Forestierr/Light_trainer/1_Documentation/Digi-Key_ Panier_files/ESP32-DEVKITC-32D_sml.jpg

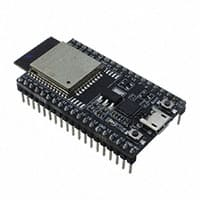
1_Documentation/Digi-Key_ Panier_files/ESP32-DEVKITC-32D_sml.jpg
