Forestierr/Light_trainer/1_Documentation/Digi-Key_ Panier_files/0805-(1.40)-CL-Series_sml.jpg

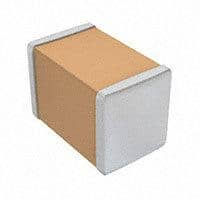
1_Documentation/Digi-Key_ Panier_files/0805-(1.40)-CL-Series_sml.jpg
