Forestierr/Light_trainer/1_Documentation/Digi-Key_ Panier_files/1101M2S5CQE2_sml.jpg

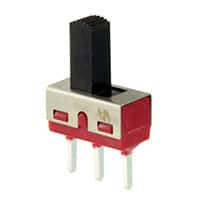
1_Documentation/Digi-Key_ Panier_files/1101M2S5CQE2_sml.jpg
