Forestierr/Light_trainer/1_Documentation/Digi-Key_ Panier_files/1210-(3225-Metric)-2,70mm_sml.jpg

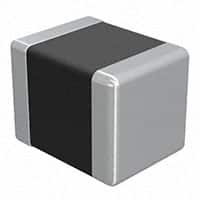
1_Documentation/Digi-Key_ Panier_files/1210-(3225-Metric)-2,70mm_sml.jpg
