Forestierr/Light_trainer/1_Documentation/Digi-Key_ Panier_files/1655_sml.JPG

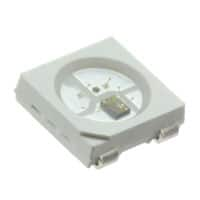
1_Documentation/Digi-Key_ Panier_files/1655_sml.JPG
