Forestierr/Light_trainer/1_Documentation/Digi-Key_ Panier_files/2464_sml.jpg

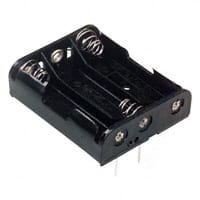
1_Documentation/Digi-Key_ Panier_files/2464_sml.jpg
