Forestierr/Light_trainer/1_Documentation/Digi-Key_ Panier_files/MX1A-11NW_sml.jpg

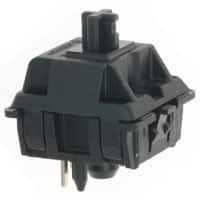
1_Documentation/Digi-Key_ Panier_files/MX1A-11NW_sml.jpg
