Forestierr/Light_trainer/1_Documentation/Digi-Key_ Panier_files/new_chat_bubble_1.jpg

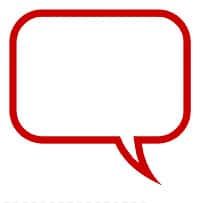
1_Documentation/Digi-Key_ Panier_files/new_chat_bubble_1.jpg
