Forestierr/Light_trainer/1_Documentation/Digi-Key_ Panier_files/RNCP1206FTD2K80_sml.jpg

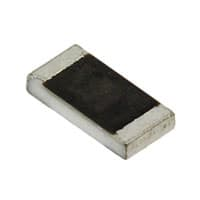
1_Documentation/Digi-Key_ Panier_files/RNCP1206FTD2K80_sml.jpg
