Forestierr/Light_trainer/1_Documentation/Digi-Key_ Panier_files/SOT223-3_sml.jpg

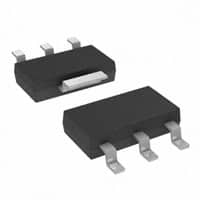
1_Documentation/Digi-Key_ Panier_files/SOT223-3_sml.jpg
