Forestierr/Light_trainer/1_Documentation/DOC_FAB/PDF_GERBER_BOT_3D.PNG

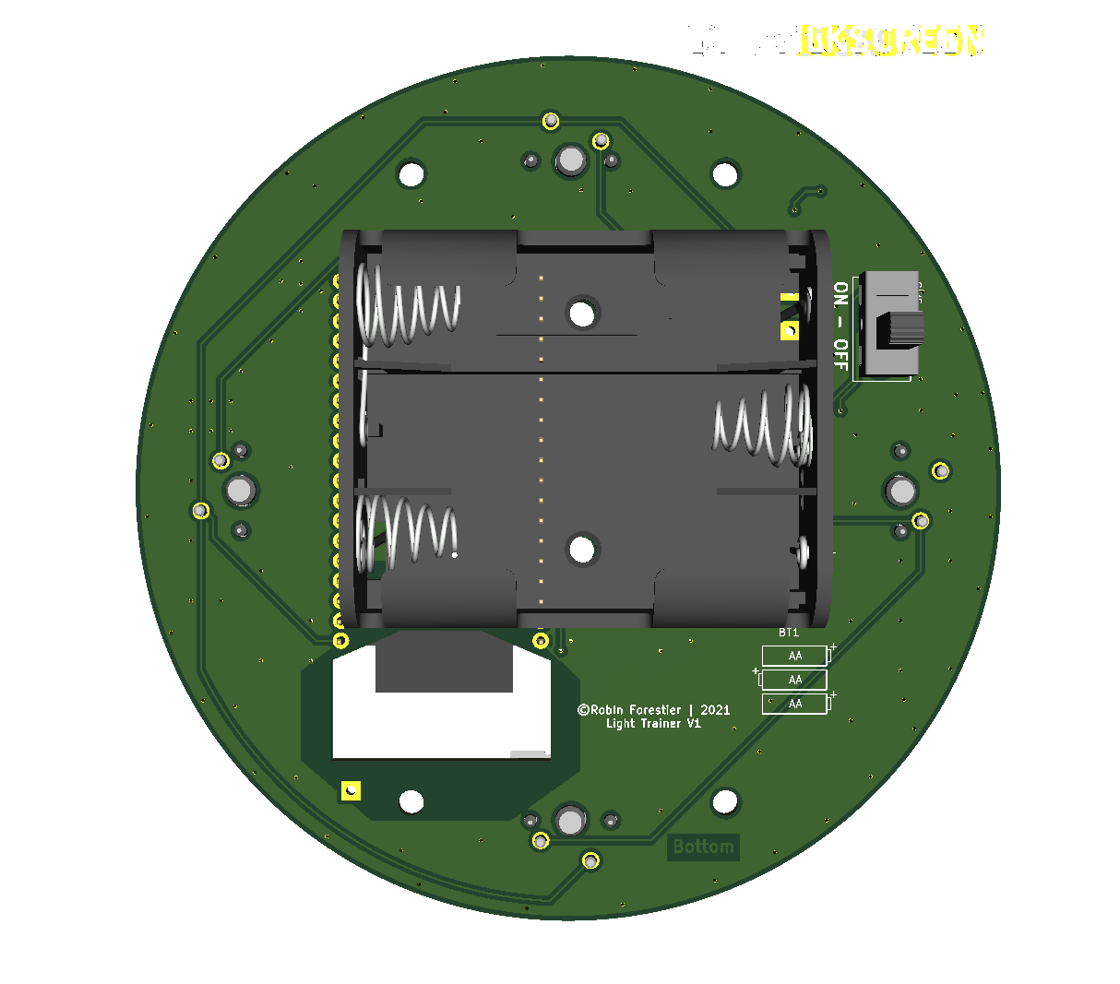
1_Documentation/DOC_FAB/PDF_GERBER_BOT_3D.PNG
