Forestierr/Light_trainer/1_Documentation/DOC_FAB/PDF_GERBER_TOP_3D.PNG

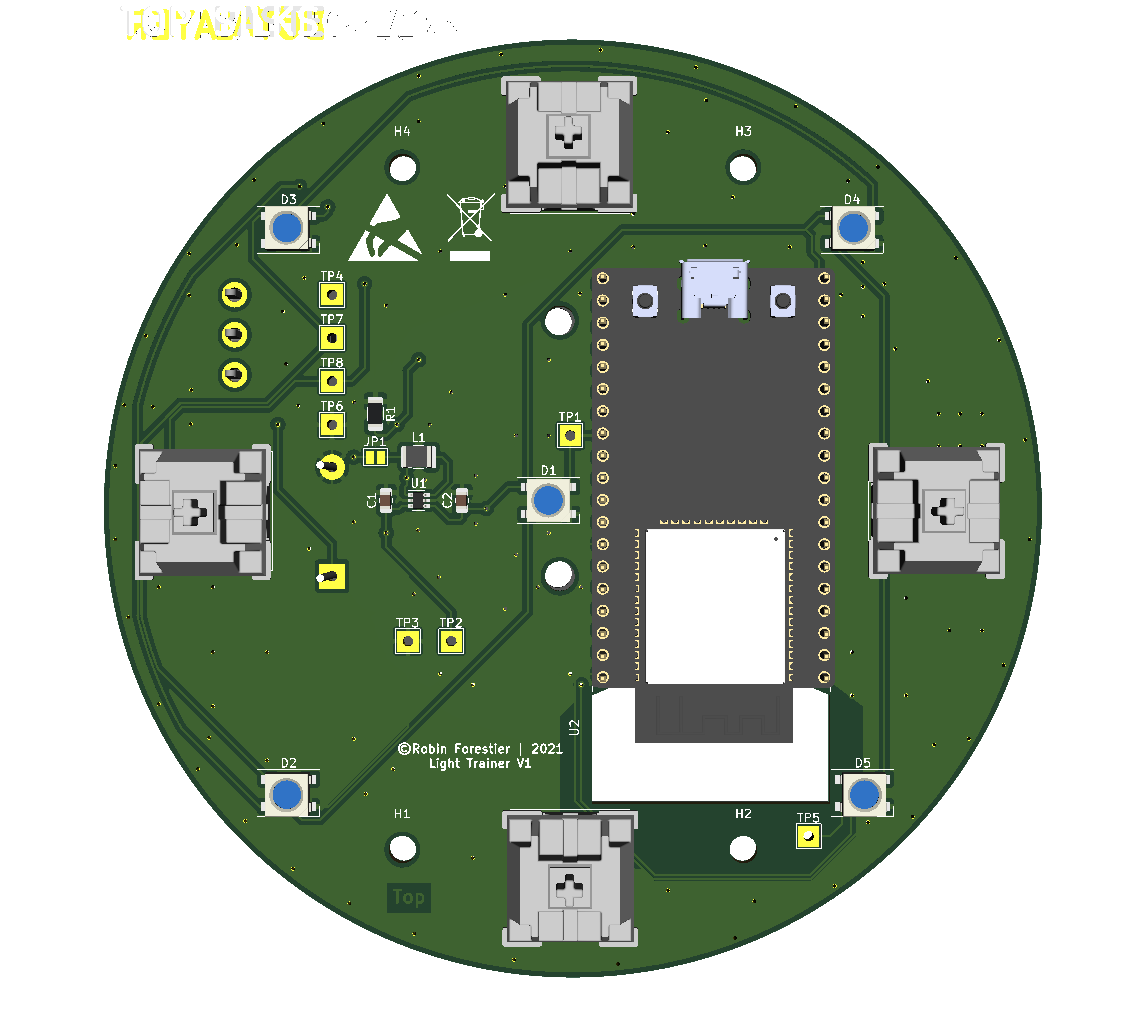
1_Documentation/DOC_FAB/PDF_GERBER_TOP_3D.PNG
