Forestierr/Light_trainer/1_Documentation/images/battery_connect.png

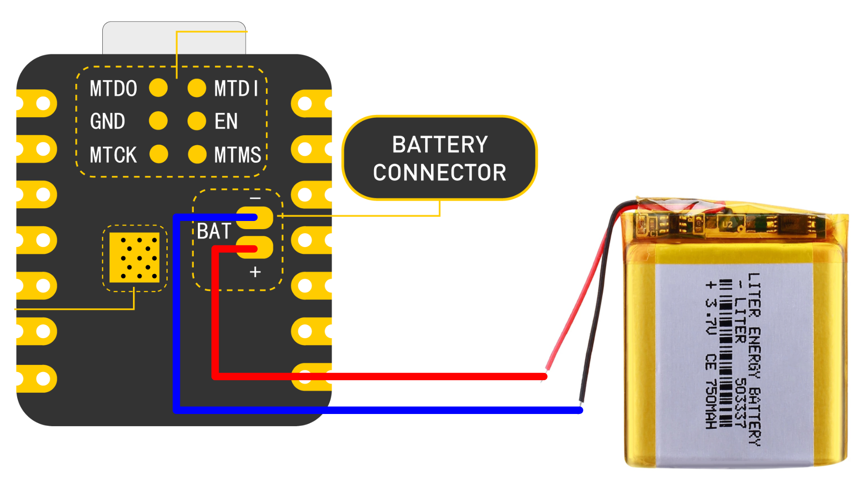
1_Documentation/images/battery_connect.png
