Forestierr/Light_trainer/1_Documentation/Photos/Conn_1.JPEG

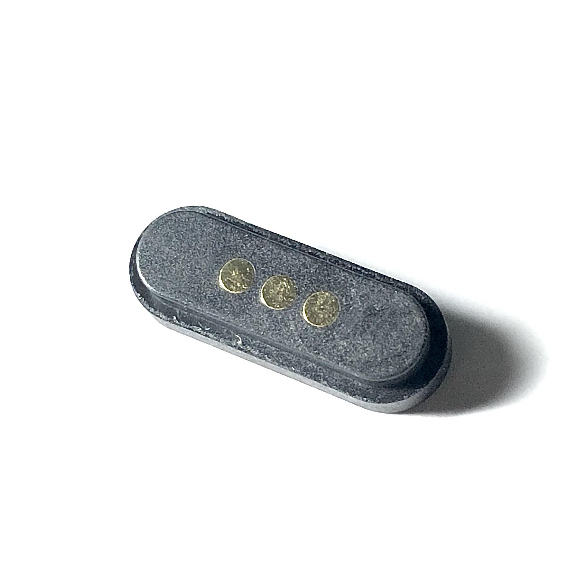
1_Documentation/Photos/Conn_1.JPEG
