Forestierr/Light_trainer/1_Documentation/Photos/Conn_4.JPEG

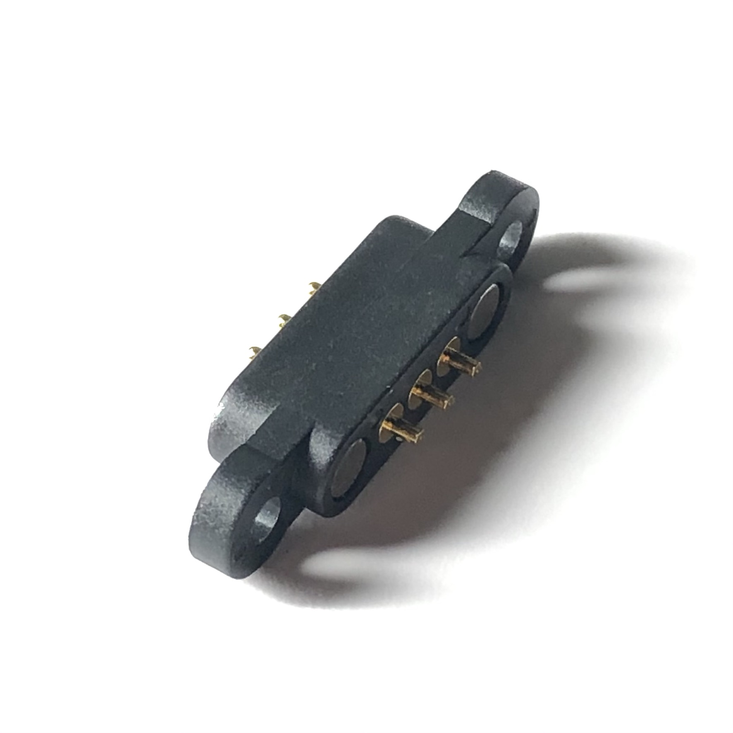
1_Documentation/Photos/Conn_4.JPEG
