Forestierr/Light_trainer/1_Documentation/Photos/Conn_5.JPEG

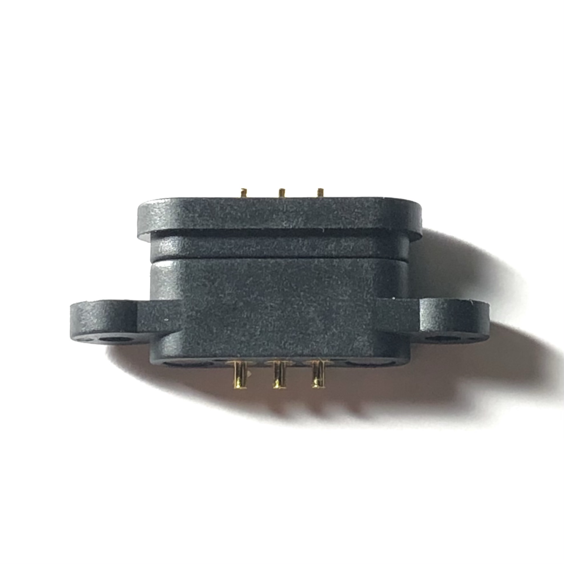
1_Documentation/Photos/Conn_5.JPEG
