Forestierr/Light_trainer/1_Documentation/Wiki/Alimentation.PNG

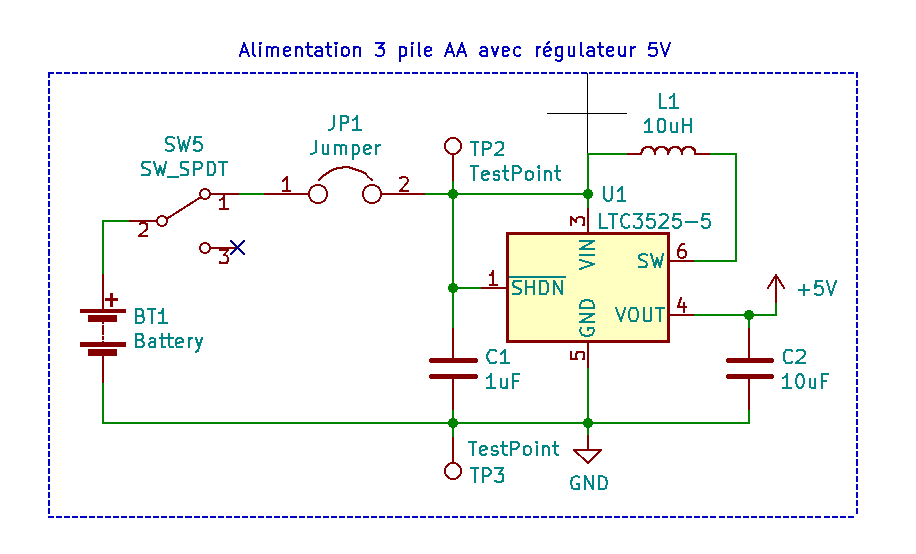
1_Documentation/Wiki/Alimentation.PNG
