Forestierr/Light_trainer/1_Documentation/Wiki/ESP.PNG

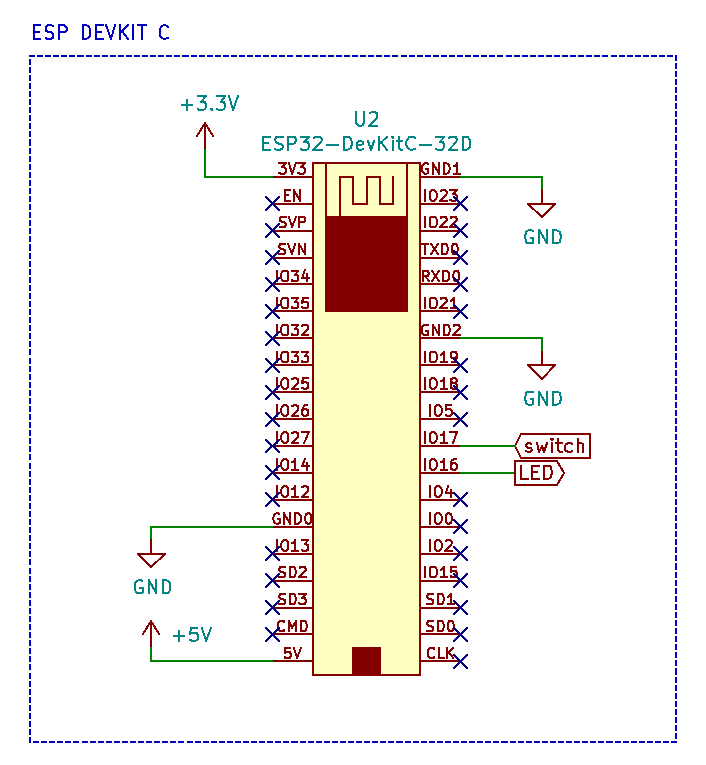
1_Documentation/Wiki/ESP.PNG
