Forestierr/Light_trainer/1_Documentation/Wiki/Led.PNG

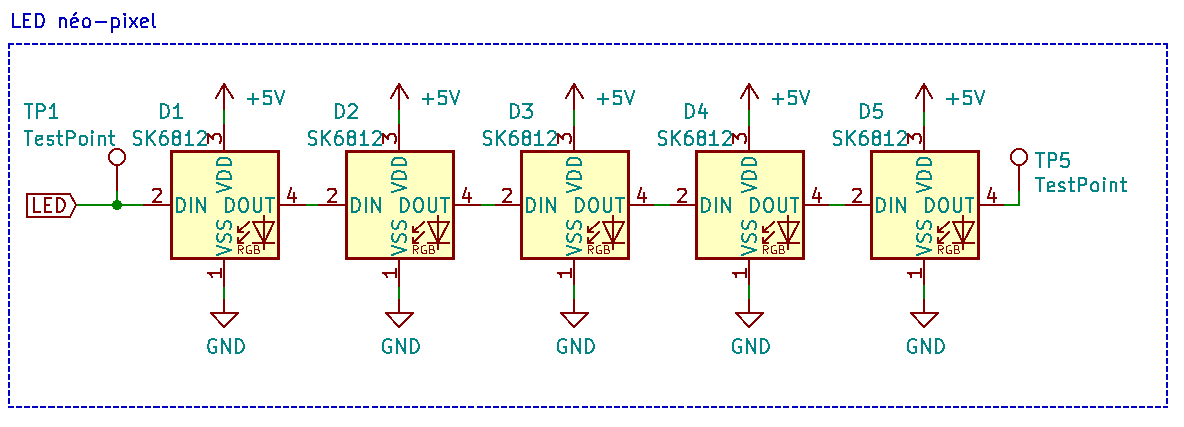
1_Documentation/Wiki/Led.PNG
