Forestierr/Light_trainer/1_Documentation/Wiki/MountingHolle.PNG

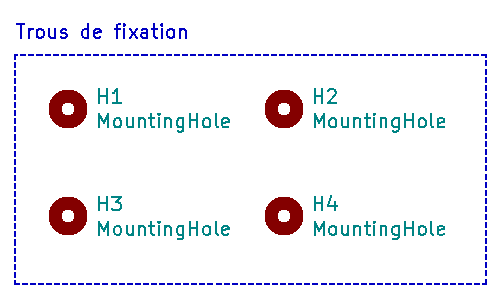
1_Documentation/Wiki/MountingHolle.PNG
