Forestierr/Light_trainer/1_Documentation/Wiki/PlanImplantation_1.jpg

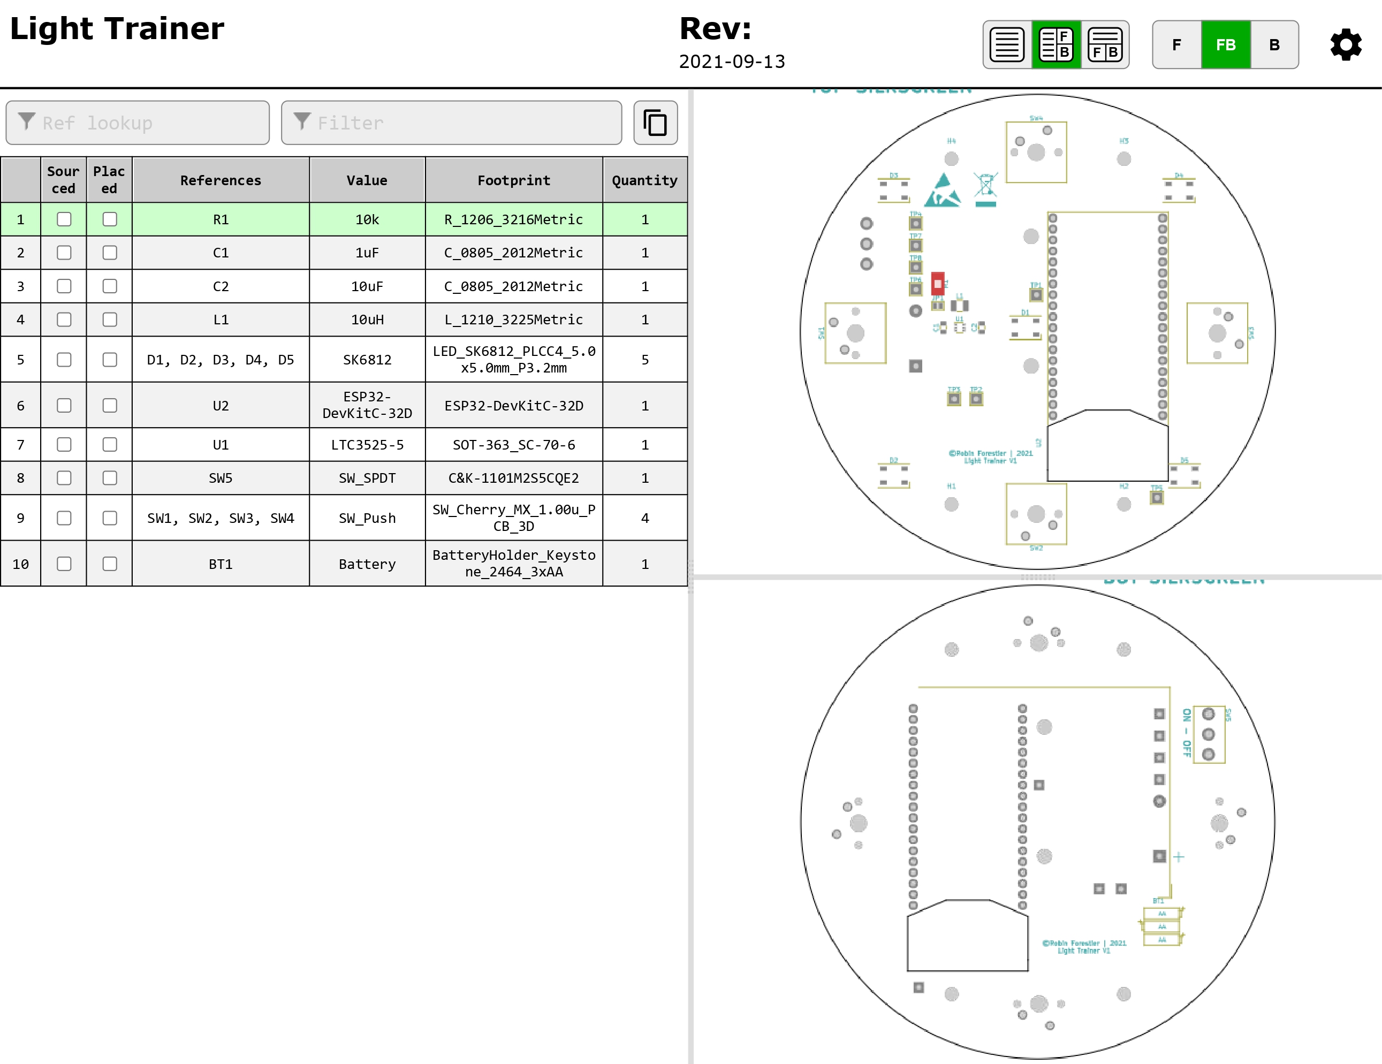
1_Documentation/Wiki/PlanImplantation_1.jpg
