Forestierr/Light_trainer/1_Documentation/Wiki/PlanImplantation_9.jpg

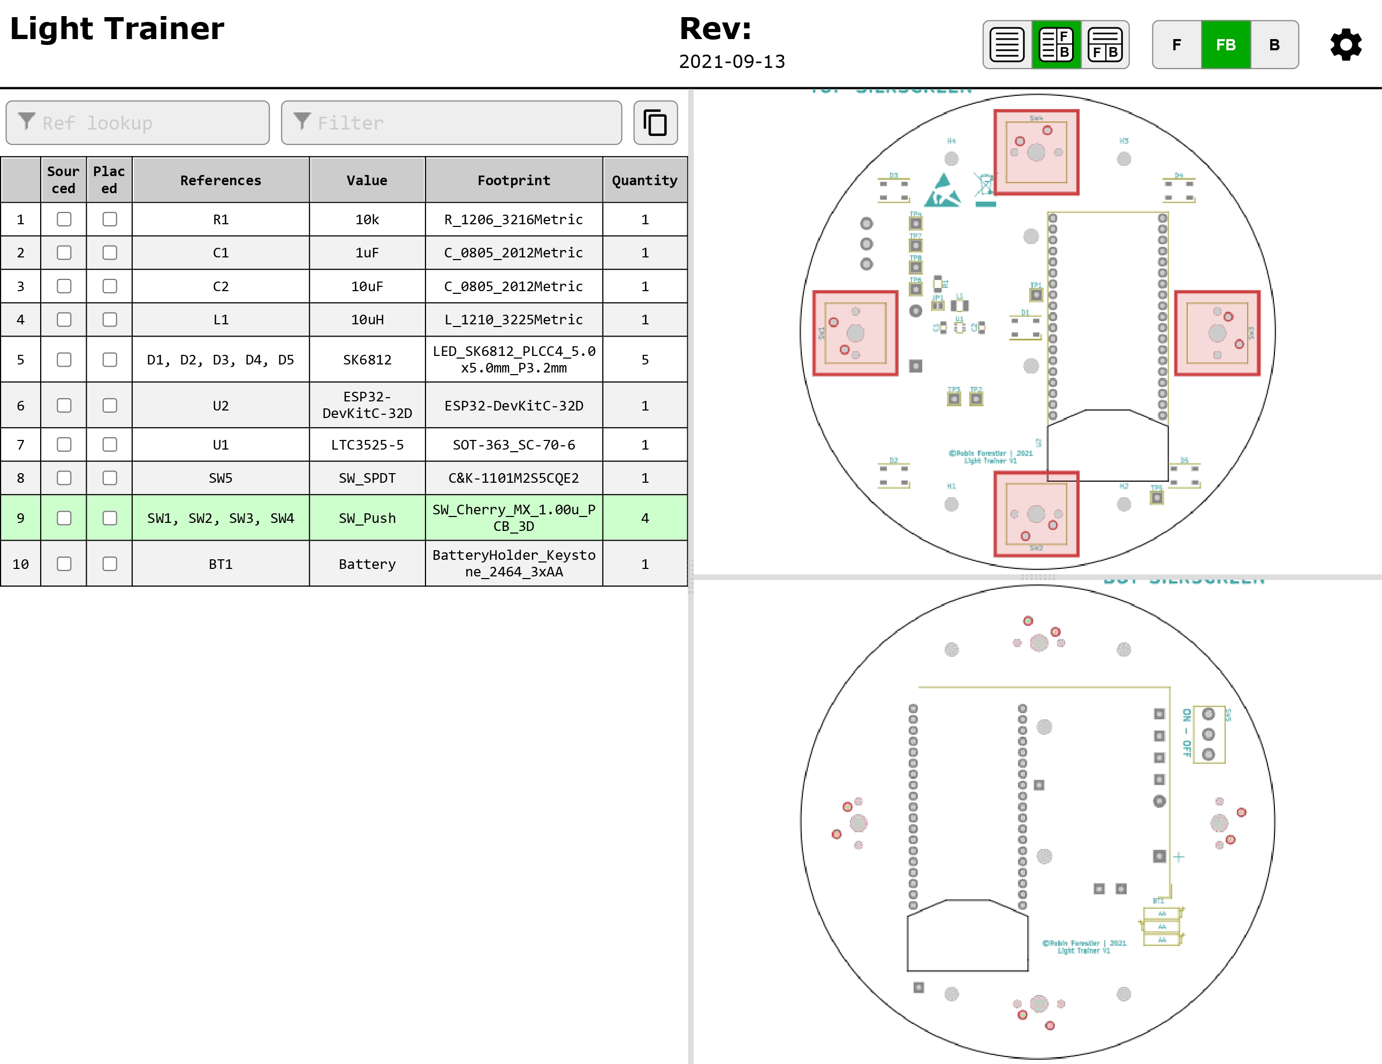
1_Documentation/Wiki/PlanImplantation_9.jpg
