Forestierr/Light_trainer/1_Documentation/Wiki/Switch.PNG

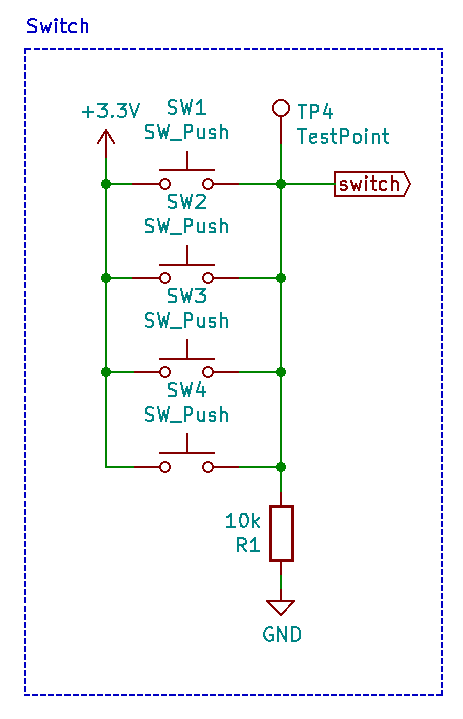
1_Documentation/Wiki/Switch.PNG
