Forestierr/Light_trainer/1_Documentation/Wiki/TestPoint.PNG

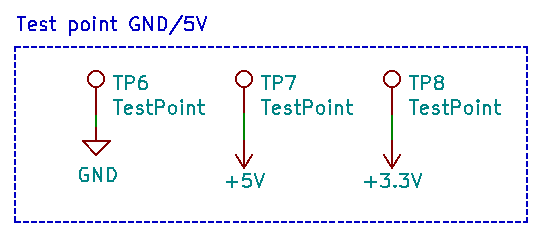
1_Documentation/Wiki/TestPoint.PNG
