Forestierr/Light_trainer/1_Documentation/DOC_FAB/PlanImplantation/PlanImplantation_1_10.pdf

Ref lookup | Filter
Light Trainer | Rev:

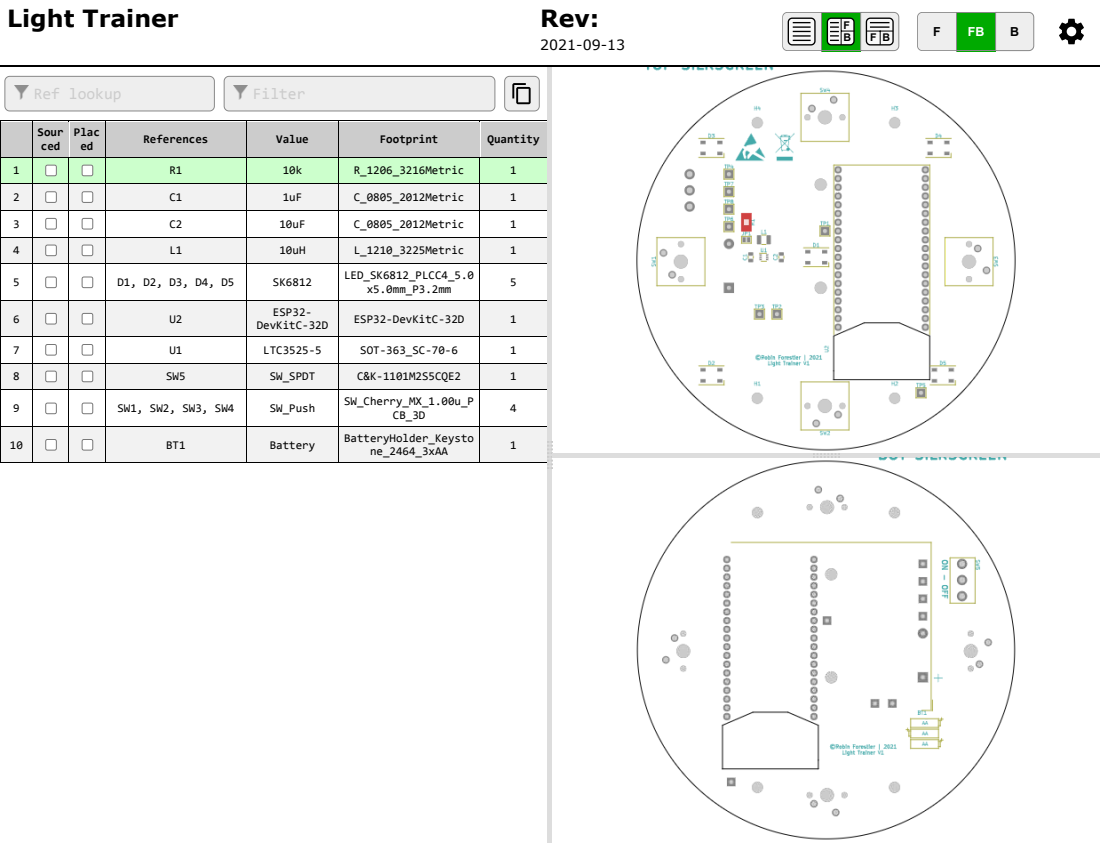
[picture p43: page 1]

Sour ced | Plac ed | References | Value | Footprint | Quantity

1 | | | R1 | 10k | R_1206_3216Metric | 1
2 | | | C1 | 1uF | C_0805_2012Metric | 1
3 | | | C2 | 10uF | C_0805_2012Metric | 1
4 | | | L1 | 10uH | L_1210_3225Metric | 1
5 | | | D1, D2, D3, D4, D5 | SK6812 | LED_SK6812_PLCC4_5.0 x5.0mm_P3.2mm | 5

6 | | | U2 | ESP32-DevKitC-32D | ESP32-DevKitC-32D | 1

7 | | | U1 | LTC3525-5 | SOT-363_SC-70-6 | 1
8 | | | SW5 | SW_SPDT | C&K-1101M2S5CQE2 | 1
9 | | | SW1, SW2, SW3, SW4 | SW_Push | SW_Cherry_MX_1.00u_P CB_3D | 4

10 | | | BT1 | Battery | BatteryHolder_Keysto ne_2464_3xAA | 1

Ref lookup | Filter

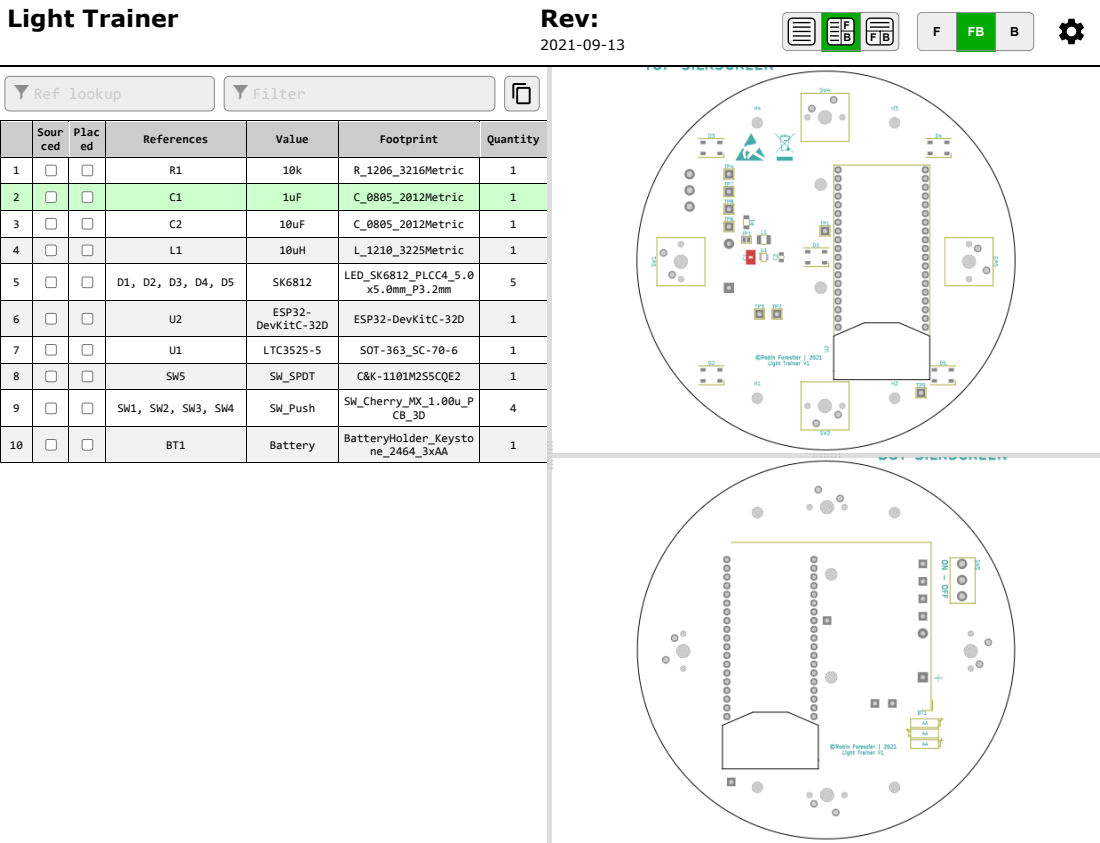
[picture p44: page 2]

Sour ced | Plac ed | References | Value | Footprint | Quantity

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

6 | | | U2 | ESP32-DevKitC-32D | ESP32-DevKitC-32D | 1

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

10 | | | BT1 | Battery | BatteryHolder_Keysto ne_2464_3xAA | 1

Ref lookup | Filter

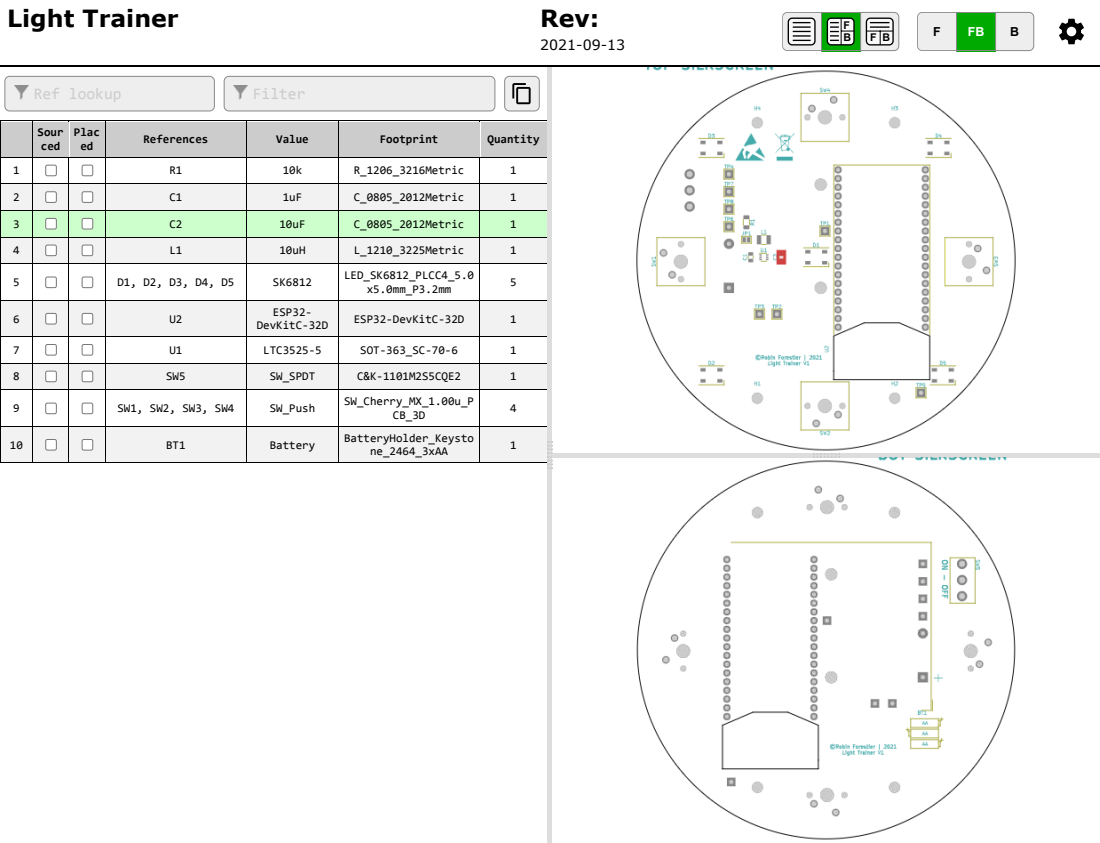
[picture p45: page 3]

Sour ced | Plac ed | References | Value | Footprint | Quantity

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

6 | | | U2 | ESP32-DevKitC-32D | ESP32-DevKitC-32D | 1

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

10 | | | BT1 | Battery | BatteryHolder_Keysto ne_2464_3xAA | 1

Ref lookup | Filter

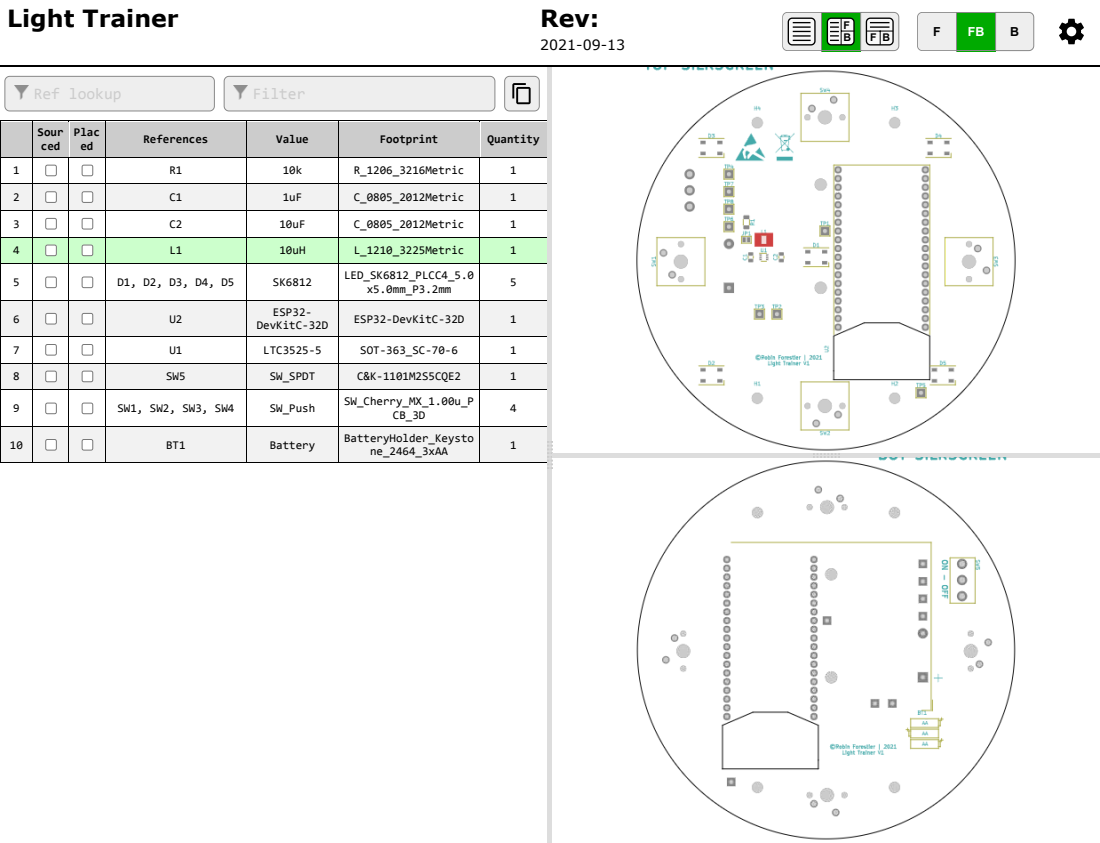
[picture p46: page 4]

Sour ced | Plac ed | References | Value | Footprint | Quantity

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

6 | | | U2 | ESP32-DevKitC-32D | ESP32-DevKitC-32D | 1

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

10 | | | BT1 | Battery | BatteryHolder_Keysto ne_2464_3xAA | 1

Ref lookup | Filter

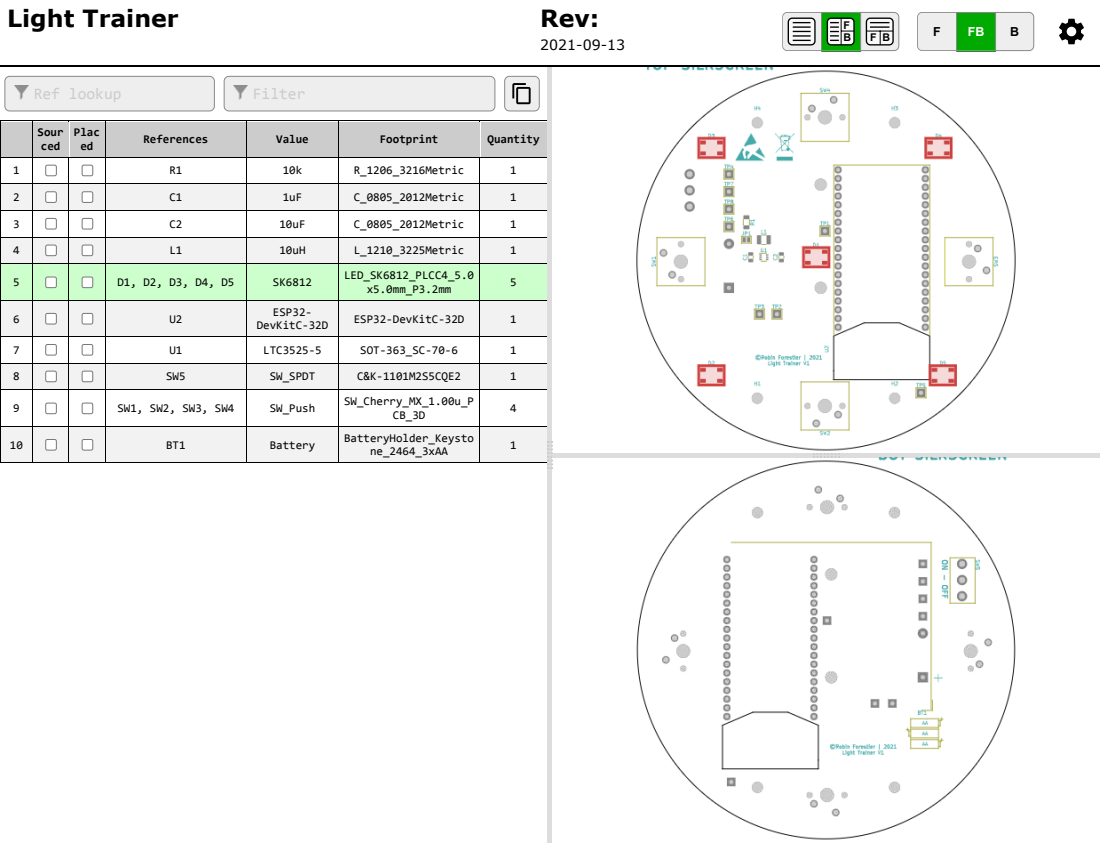
[picture p47: page 5]

Sour ced | Plac ed | References | Value | Footprint | Quantity

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

6 | | | U2 | ESP32-DevKitC-32D | ESP32-DevKitC-32D | 1

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

10 | | | BT1 | Battery | BatteryHolder_Keysto ne_2464_3xAA | 1

Ref lookup | Filter

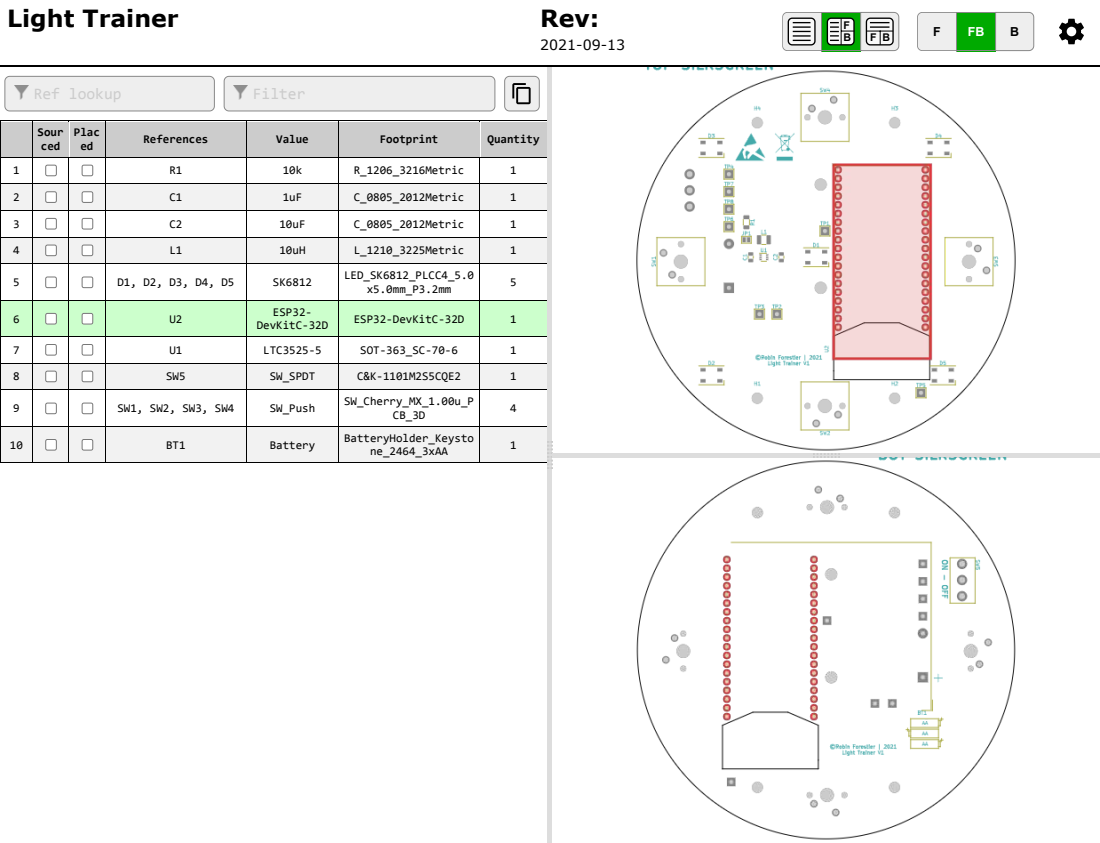
[picture p48: page 6]

Sour ced | Plac ed | References | Value | Footprint | Quantity

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

6 | | | U2 | ESP32-DevKitC-32D | ESP32-DevKitC-32D | 1

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

10 | | | BT1 | Battery | BatteryHolder_Keysto ne_2464_3xAA | 1

Ref lookup | Filter

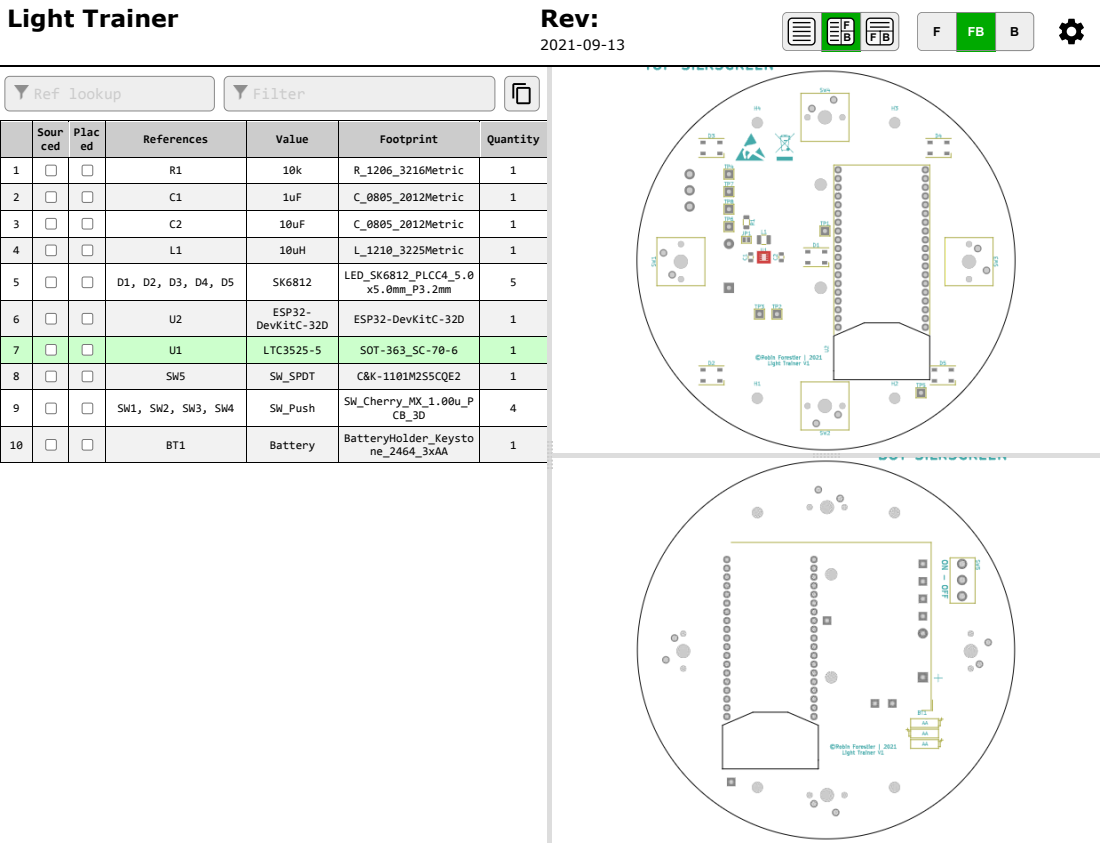
[picture p49: page 7]

Sour ced | Plac ed | References | Value | Footprint | Quantity

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

6 | | | U2 | ESP32-DevKitC-32D | ESP32-DevKitC-32D | 1

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

10 | | | BT1 | Battery | BatteryHolder_Keysto ne_2464_3xAA | 1

Ref lookup | Filter

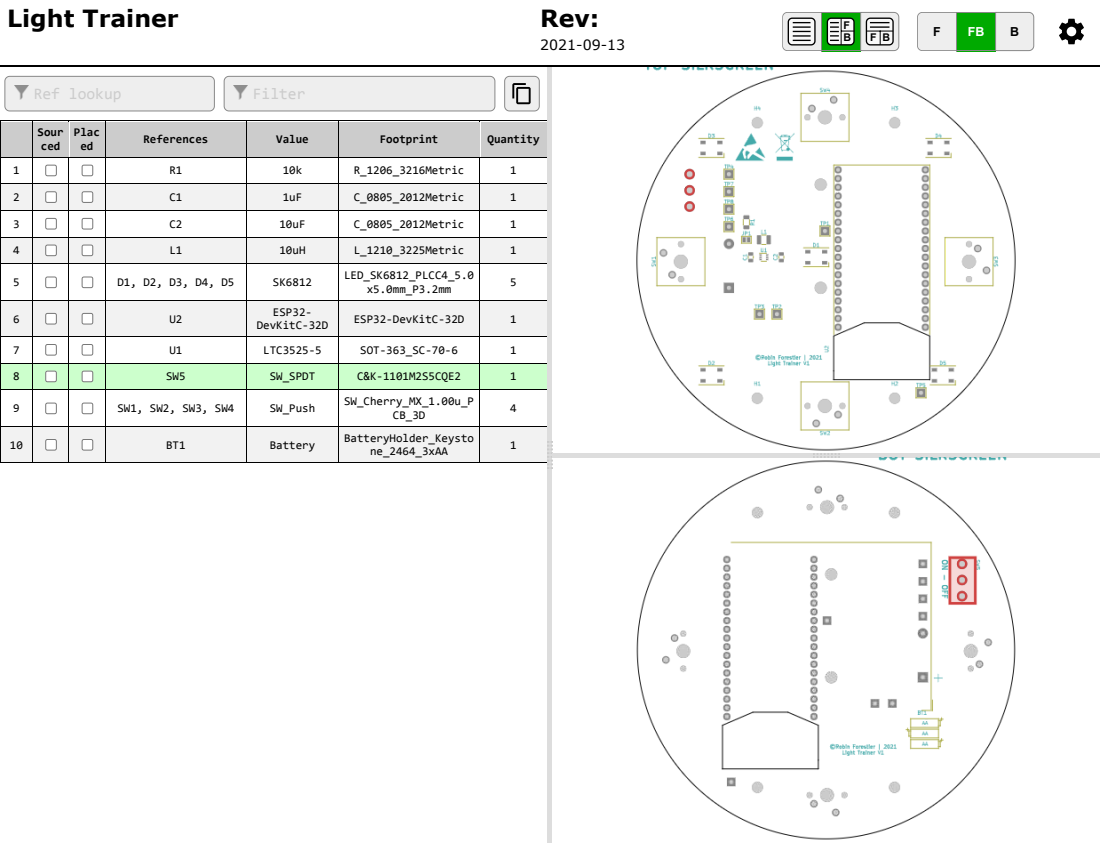
[picture p50: page 8]

Sour ced | Plac ed | References | Value | Footprint | Quantity

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

6 | | | U2 | ESP32-DevKitC-32D | ESP32-DevKitC-32D | 1

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

10 | | | BT1 | Battery | BatteryHolder_Keysto ne_2464_3xAA | 1

Ref lookup | Filter

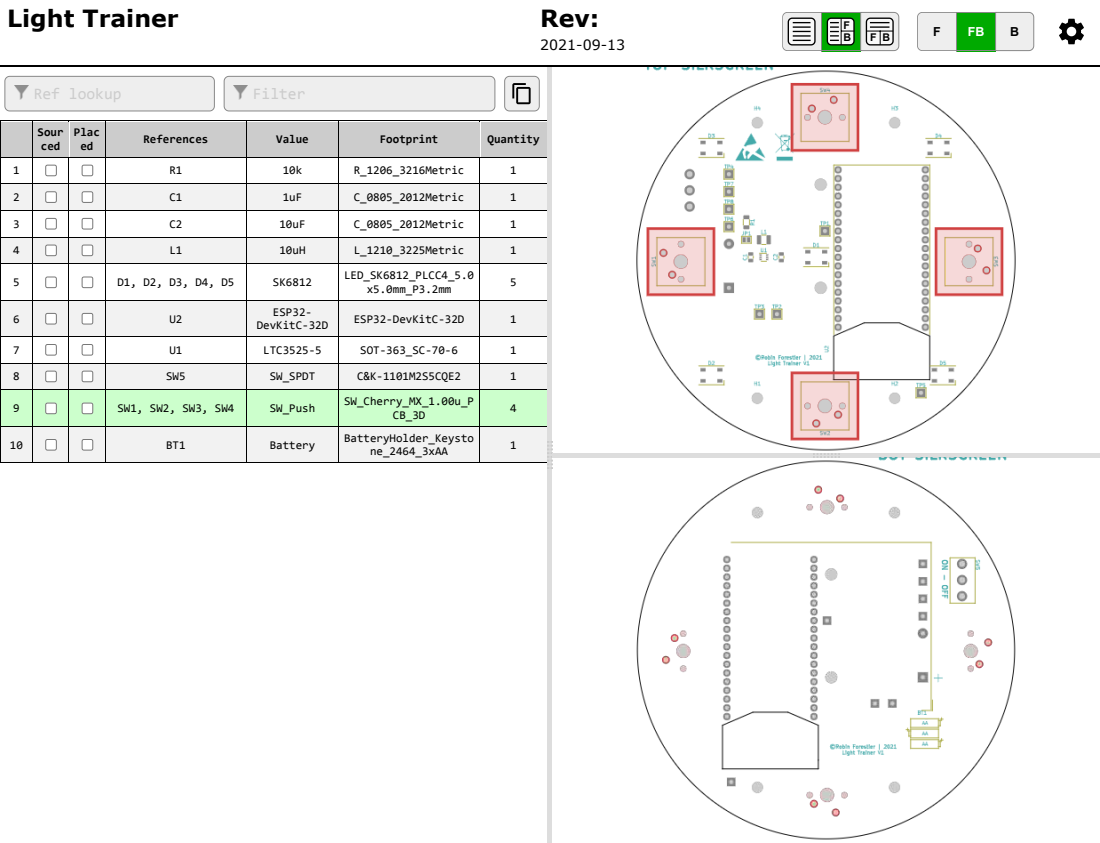
[picture p51: page 9]

Sour ced | Plac ed | References | Value | Footprint | Quantity

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

6 | | | U2 | ESP32-DevKitC-32D | ESP32-DevKitC-32D | 1

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

10 | | | BT1 | Battery | BatteryHolder_Keysto ne_2464_3xAA | 1

Ref lookup | Filter

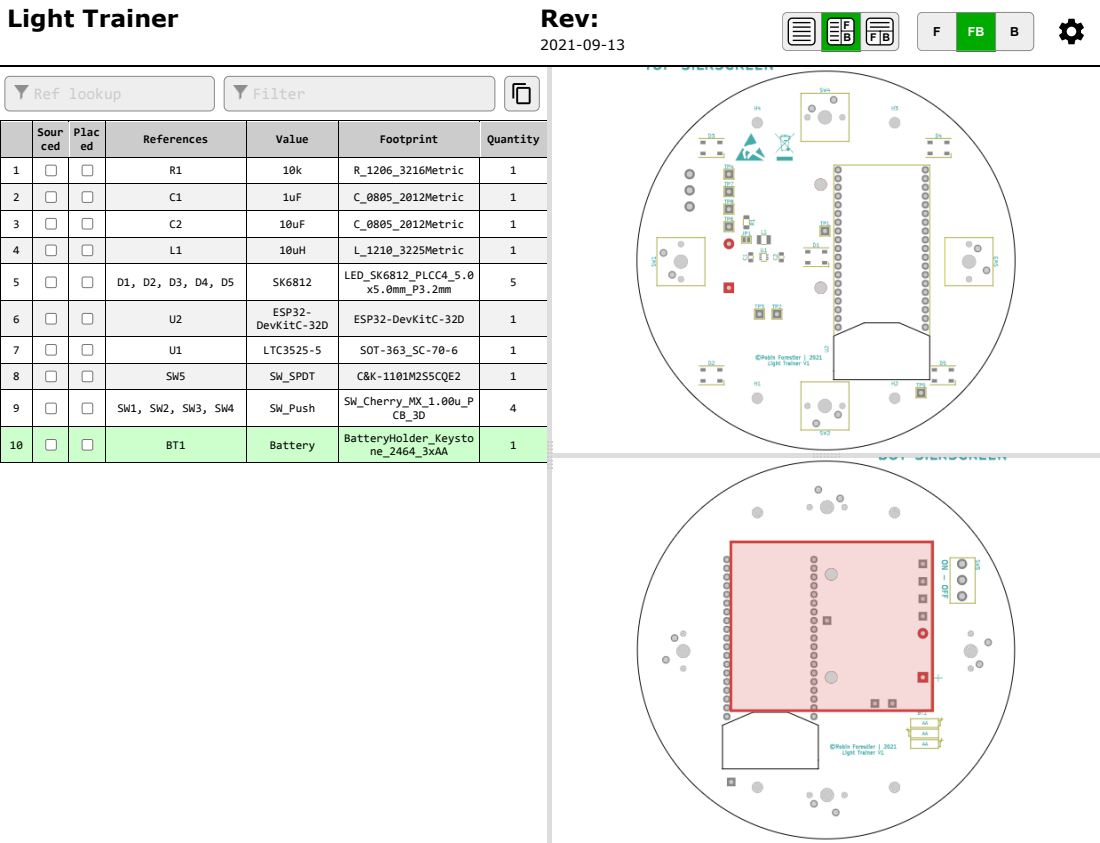
[picture p52: page 10]

Sour ced | Plac ed | References | Value | Footprint | Quantity

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

6 | | | U2 | ESP32-DevKitC-32D | ESP32-DevKitC-32D | 1

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

10 | | | BT1 | Battery | BatteryHolder_Keysto ne_2464_3xAA | 1
