Forestierr/Light_trainer/5_Programmation/XIAO-esp32-v3/main/DashboardHtml.h

#ifndef DASHBOARDHTML_H
#define DASHBOARDHTML_H

#include <Arduino.h>

// Dashboard Web Light Trainer - HTML5/CSS3/JS pré-compressé GZIP
// Taille originale: 84219 octets | Taille GZIP: 18264 octets (21.7%)
const size_t DASHBOARD_HTML_GZ_LEN = 18264;
const uint8_t DASHBOARD_HTML_GZ[] PROGMEM = {
  0x1F, 0x8B, 0x08, 0x00, 0x00, 0x00, 0x00, 0x00, 0x02, 0xFF, 0xED, 0x7D, 0x5D, 0x73, 0xDB, 0x48,
  0x92, 0xE0, 0xBB, 0x7F, 0x45, 0x99, 0xD3, 0xDD, 0x24, 0xC7, 0x22, 0x45, 0x80, 0xA4, 0x2C, 0x4B,
  0xB6, 0xE6, 0x64, 0x89, 0xB6, 0x35, 0x2B, 0x59, 0x5A, 0x91, 0xF6, 0x6C, 0x6F, 0x47, 0x5F, 0x1B,
  0x22, 0x21, 0x12, 0xD3, 0x20, 0xC1, 0x01, 0x40, 0x59, 0x6A, 0x8F, 0x22, 0xFA, 0xE5, 0x22, 0xAE,
  0xEF, 0x1E, 0x2E, 0xE2, 0x6E, 0x9F, 0x36, 0x36, 0x62, 0xF7, 0x36, 0xEE, 0x61, 0x7C, 0x0F, 0xF7,
  0x7C, 0x77, 0xAF, 0xFA, 0x27, 0xFD, 0x07, 0xEE, 0x7E, 0xC2, 0x65, 0x66, 0x15, 0x80, 0x2A, 0xA0,
  0x00, 0x82, 0xB2, 0xEC, 0x76, 0x5F, 0x4C, 0x7F, 0x50, 0x24, 0x50, 0x95, 0x95, 0x55, 0x95, 0x95,
  0x99, 0x95, 0x99, 0x95, 0xF5, 0xF8, 0xFE, 0xFE, 0xF1, 0xDE, 0xE0, 0xEB, 0x93, 0x1E, 0x9B, 0x84,
  0x53, 0x77, 0xE7, 0xDE, 0x63, 0xFC, 0xC3, 0x5C, 0x6B, 0x36, 0x7E, 0x52, 0x39, 0xF7, 0x2B, 0xF8,
  0xC0, 0xB6, 0x46, 0x3B, 0xF7, 0x18, 0x7B, 0x3C, 0xB5, 0x43, 0x8B, 0x0D, 0x27, 0x96, 0x1F, 0xD8,
  0xE1, 0x93, 0xCA, 0xAB, 0xC1, 0xB3, 0xC6, 0x66, 0x25, 0x79, 0x31, 0xB3, 0xA6, 0xF6, 0x93, 0xCA,
  0x85, 0x63, 0xBF, 0x9D, 0x7B, 0x7E, 0x58, 0x61, 0x43, 0x6F, 0x16, 0xDA, 0x33, 0x28, 0xF8, 0xD6,
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
  0xE2, 0xCC, 0x1B, 0x5D, 0xC5, 0xB4, 0x79, 0x06, 0x94, 0x3E, 0xF6, 0xBD, 0xC5, 0x6C, 0x14, 0xD5,
  0xB8, 0xB0, 0xFC, 0x1A, 0x52, 0x6C, 0xDC, 0x03, 0xE5, 0x39, 0x1F, 0x8F, 0xF8, 0xDD, 0x39, 0x2C,
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
};

#endif // DASHBOARDHTML_H
