Forestierr/Light_trainer/5_Programmation/Version_03/Playground classic test/sketch_jan21a/sketch_jan21a.ino

// SPDX-FileCopyrightText: 2017 Limor Fried for Adafruit Industries
//
// SPDX-License-Identifier: MIT

#include <Adafruit_CircuitPlayground.h>

void setup() {
  // Initialize the circuit playground
  CircuitPlayground.begin();
}

void loop() {
  // If the left button is pressed....
  if (CircuitPlayground.leftButton() || CircuitPlayground.rightButton()) {
      CircuitPlayground.redLED(HIGH);  // LED on
      CircuitPlayground.playTone(440, 100); // sound on
  } else {
      CircuitPlayground.redLED(LOW);   // LED off
  }
}
